MakeMagazinDE/MuscleLaserRun/EAGLE_Schaltplan.sch

## EAGLE design EAGLE_Schaltplan.sch (2019-12-09)

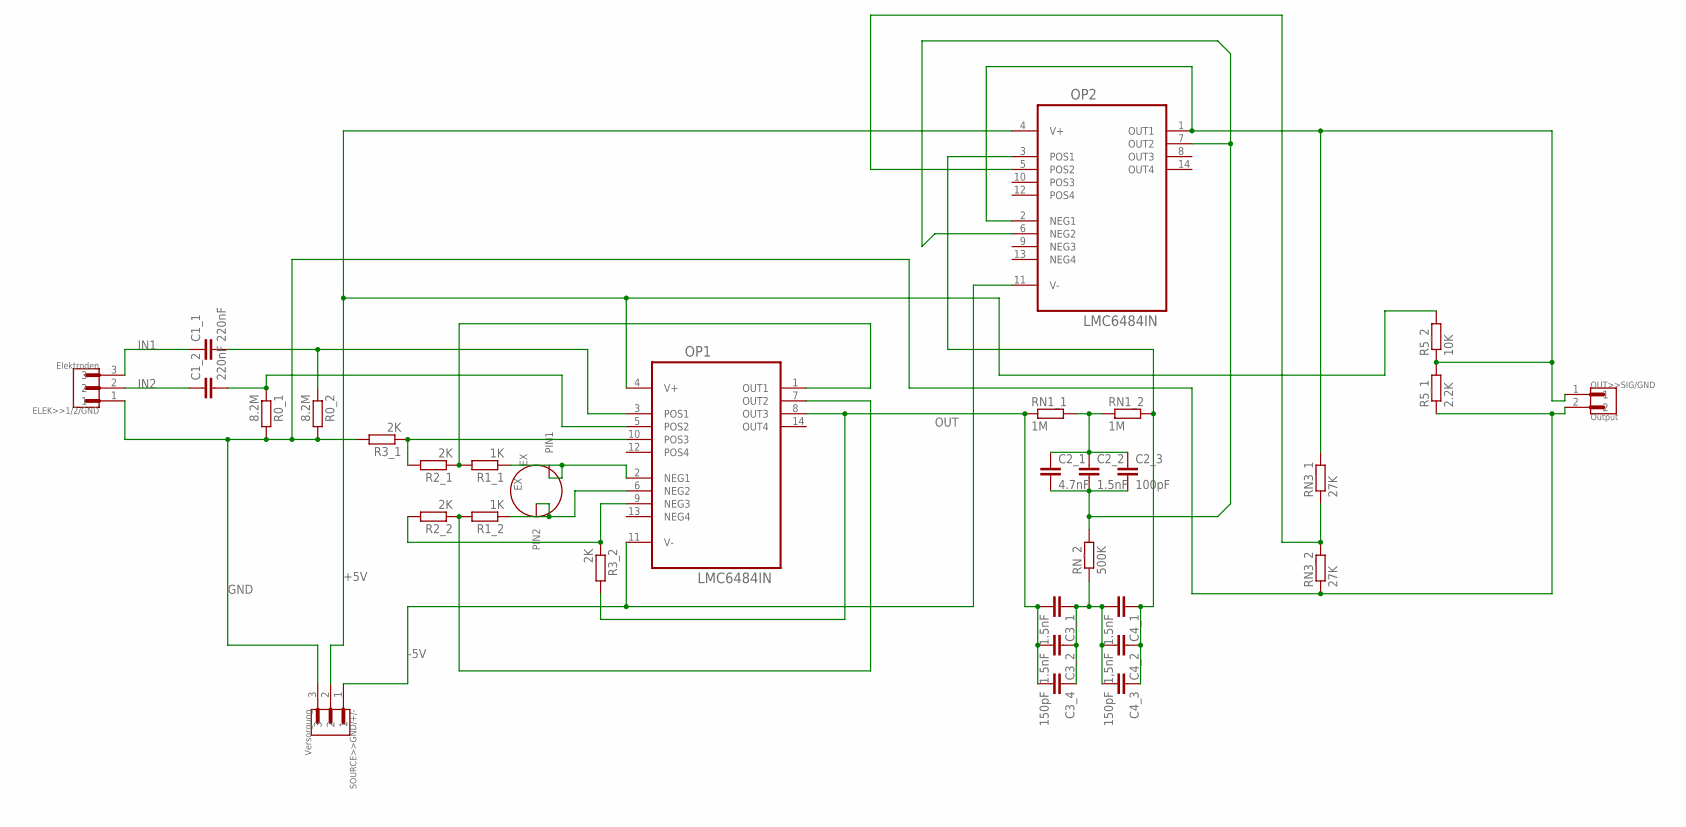
[picture p6: schematic EAGLE_Schaltplan.sch]

Parts:
C1_1, C1_2: 220nF; C050-024X044
C2_1: 4.7nF; C050-024X044
C2_2, C3_1, C3_2, C4_1: 1.5nF; C050-024X044
C2_3: 100pF; C050-024X044
C3_4, C4_3: 150pF; C050-024X044
C4_2: 1,5nF; C050-024X044
ELEK>>1/2/GND: Elektroden; JST_B3P-VH(LF)(SN)
OP1, OP2: LMC6484IN; DIP254P762X508-14
OUT>>SIG/GND: Output; JST_B2P-VH(LF)(SN)
POTI_1K: 1K; MOLEX_2PIN_SIDE
R0_1, R0_2: 8.2M; 0207/7
R1_1, R1_2: 1K; 0207/7
R2_1, R2_2, R3_1, R3_2: 2K; 0207/7
R5_1: 2.2K; 0207/7
R5_2: 10K; 0207/7
RN1_1, RN1_2: 1M; 0207/7
RN3_1, RN3_2: 27K; 0207/7
RN_2: 500K; 0207/7
SOURCE>>GND/+/-: Versorgung; JST_B3P-VH(LF)(SN)

Connections:
+5V: OP1.4 (V+), OP2.4 (V+), R5_2.2, SOURCE>>GND/+/-.2
-5V: OP1.11 (V-), OP2.11 (V-), SOURCE>>GND/+/-.1
GND: ELEK>>1/2/GND.1, OUT>>SIG/GND.2, R0_1.2, R0_2.2, R3_1.2, R5_1.1, RN3_2.1, SOURCE>>GND/+/-.3
IN1: C1_1.1, ELEK>>1/2/GND.3
IN2: C1_2.1, ELEK>>1/2/GND.2
unnamed: OP1.2 (NEG1), POTI_1K.P$1 (PIN1), R1_1.1
unnamed: OP1.6 (NEG2), POTI_1K.P$2 (PIN2), R1_2.1
unnamed: OP1.7 (OUT2), R1_2.2, R2_2.1
unnamed: OP1.1 (OUT1), R1_1.2, R2_1.1
unnamed: OP1.10 (POS3), R2_1.2, R3_1.1
unnamed: OP1.9 (NEG3), R2_2.2, R3_2.1
unnamed: C2_1.1, C2_2.1, C2_3.1, RN1_1.2, RN1_2.1
unnamed: OP2.1 (OUT1), OP2.2 (NEG1), OUT>>SIG/GND.1, R5_1.2, R5_2.1, RN3_1.2
unnamed: C1_2.2, OP1.5 (POS2), R0_1.1
unnamed: C1_1.2, OP1.3 (POS1), R0_2.1
unnamed: C2_1.2, C2_2.2, C2_3.2, OP2.6 (NEG2), OP2.7 (OUT2), RN_2.2
unnamed: OP2.5 (POS2), RN3_1.1, RN3_2.2
unnamed: C3_1.1, C3_2.1, C3_4.1, C4_1.2, C4_2.2, C4_3.2, RN_2.1
unnamed: C4_1.1, C4_2.1, C4_3.1, OP2.3 (POS1), RN1_2.2
OUT: C3_1.2, C3_2.2, C3_4.2, OP1.8 (OUT3), R3_2.2, RN1_1.1
